MiyuYamasaki-Davis/EE-Emerge-2023-DancePad/pictures/Encasement/IMG_6620 2.JPG

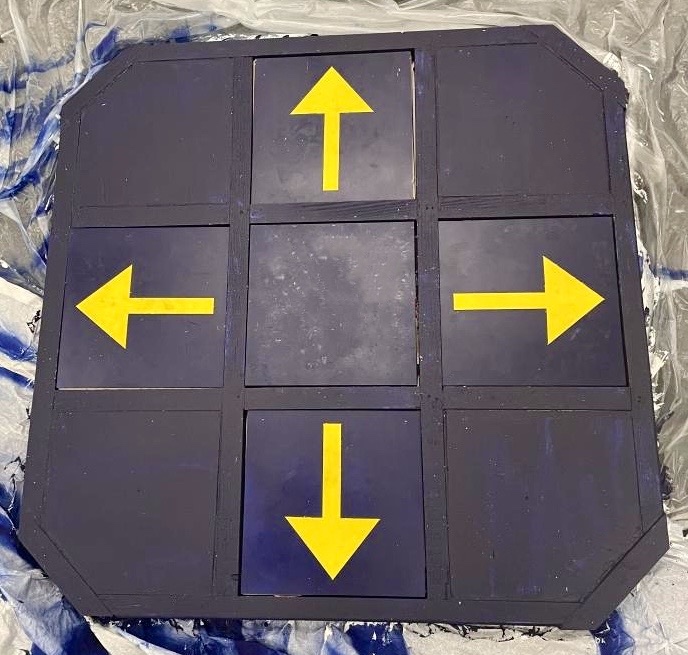
pictures/Encasement/IMG_6620 2.JPG
