MiyuYamasaki-Davis/EE-Emerge-2023-DancePad/pictures/Encasement/paintedBoard.JPG

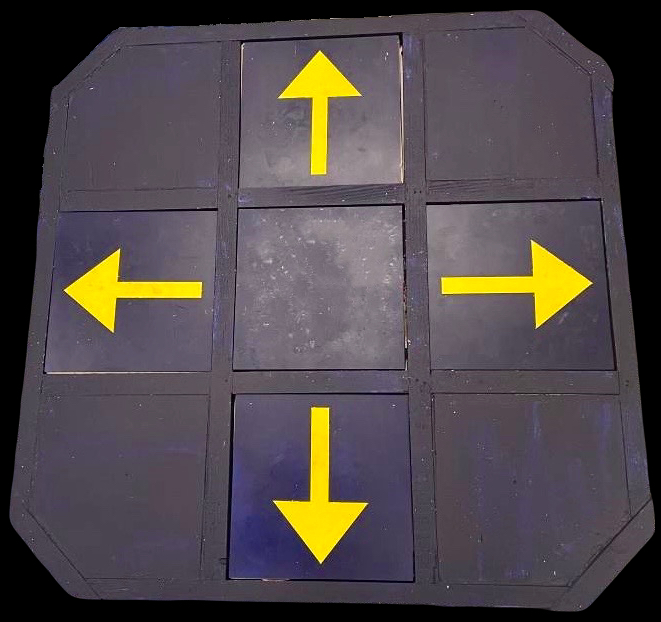
pictures/Encasement/paintedBoard.JPG
