MiyuYamasaki-Davis/EE-Emerge-2023-DancePad/pictures/Encasement/v1 plate sample.jpg

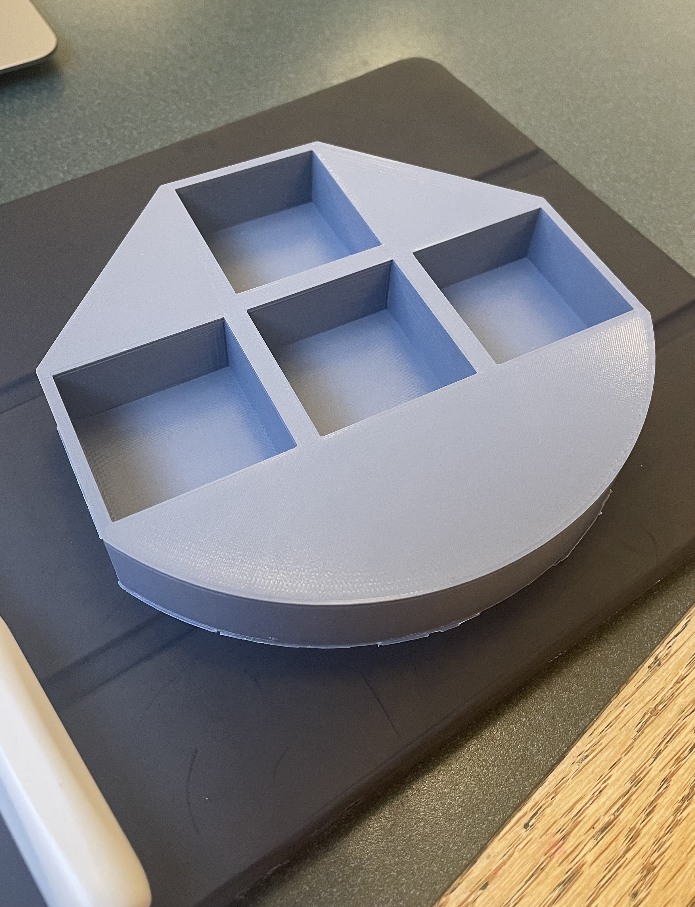
pictures/Encasement/v1 plate sample.jpg
