MiyuYamasaki-Davis/EE-Emerge-2023-DancePad/pictures/Encasement/v2 plate model.png

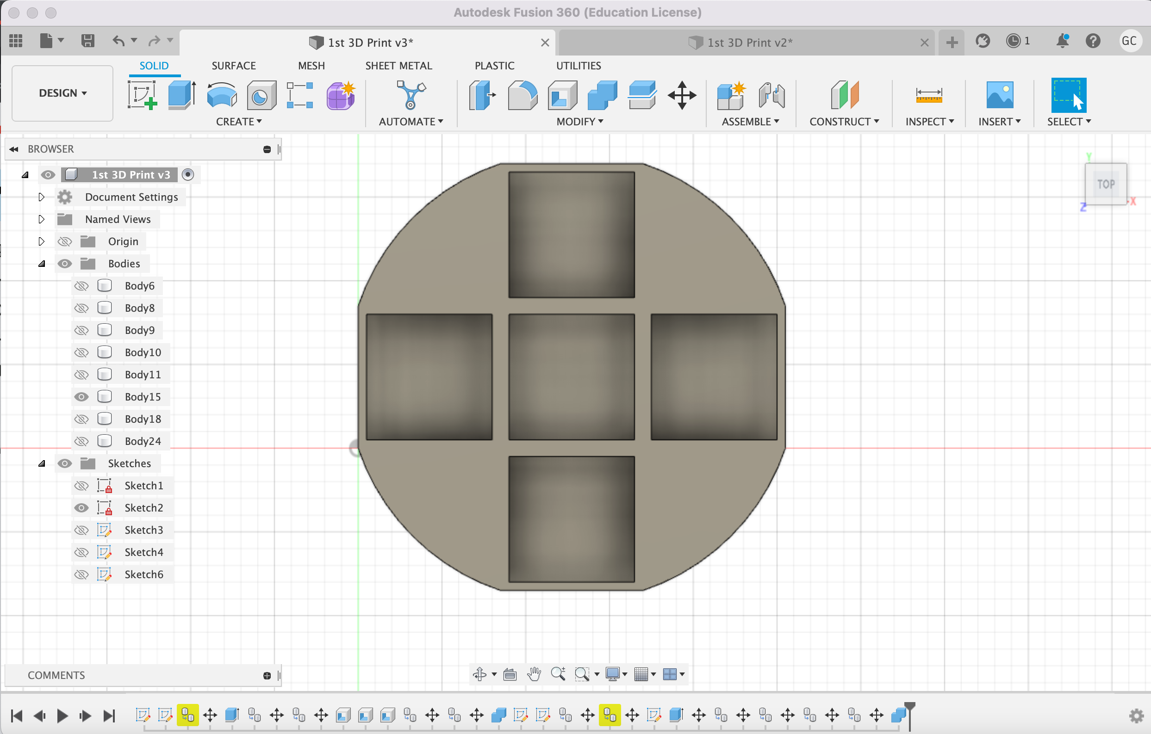
pictures/Encasement/v2 plate model.png
