MiyuYamasaki-Davis/EE-Emerge-2023-DancePad/pictures/Encasement/v3 platform design finished.jpg

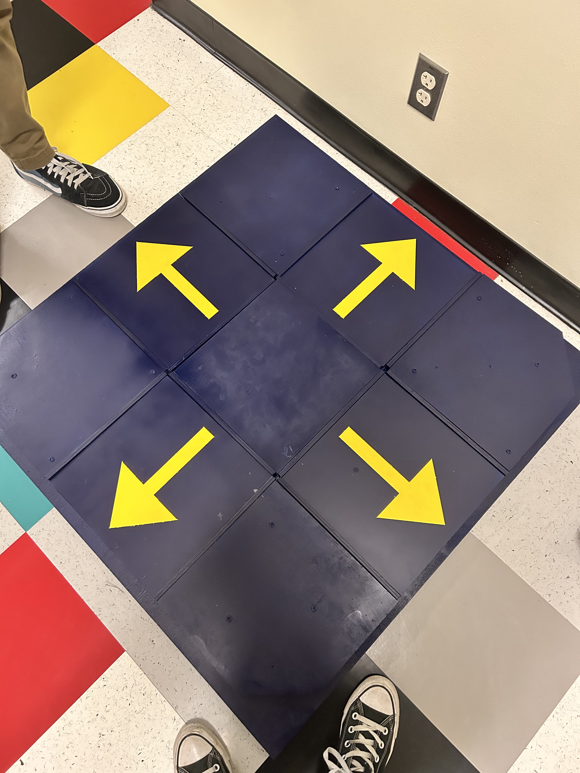
pictures/Encasement/v3 platform design finished.jpg
