MiyuYamasaki-Davis/EE-Emerge-2023-DancePad/pictures/Hardware/PCB v3 layout.png

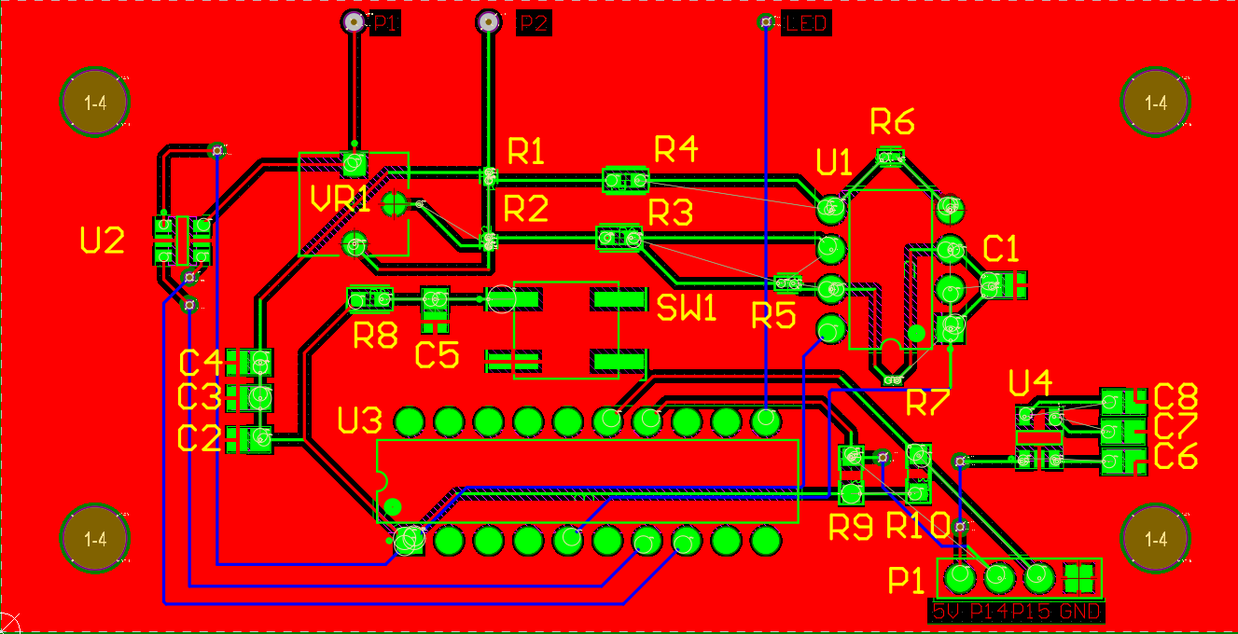
pictures/Hardware/PCB v3 layout.png
