MiyuYamasaki-Davis/EE-Emerge-2023-DancePad/pictures/Hardware/PCB v3 page 1.png

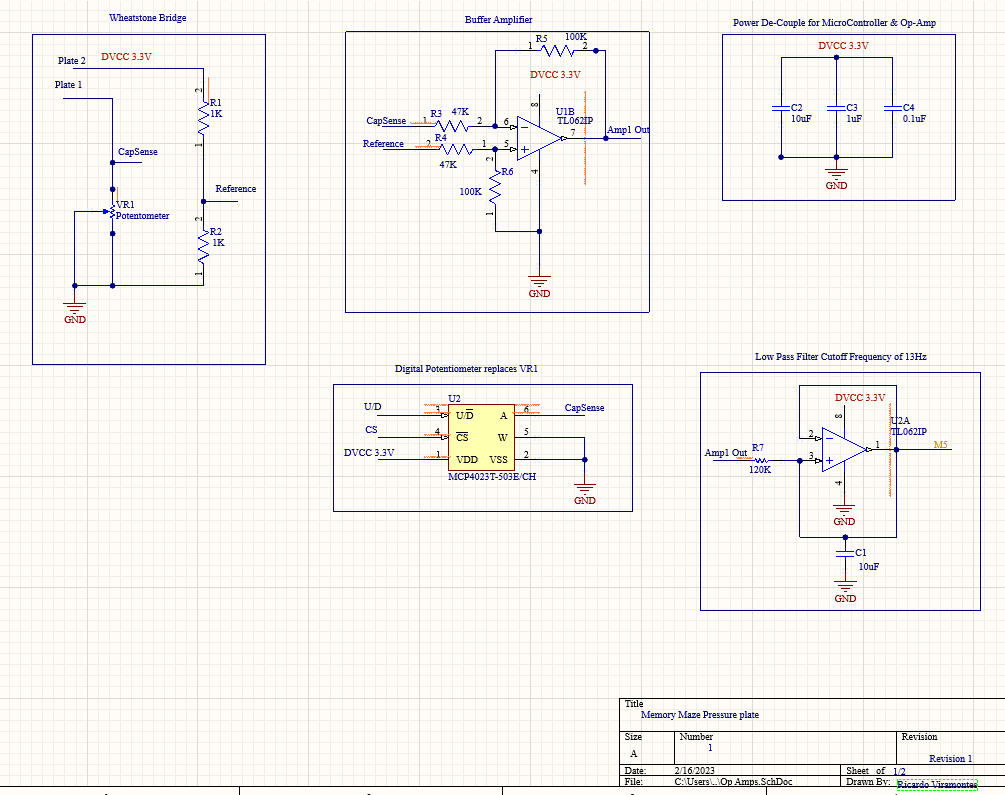
pictures/Hardware/PCB v3 page 1.png
