MiyuYamasaki-Davis/EE-Emerge-2023-DancePad/pictures/Hardware/PCB v4.jpg

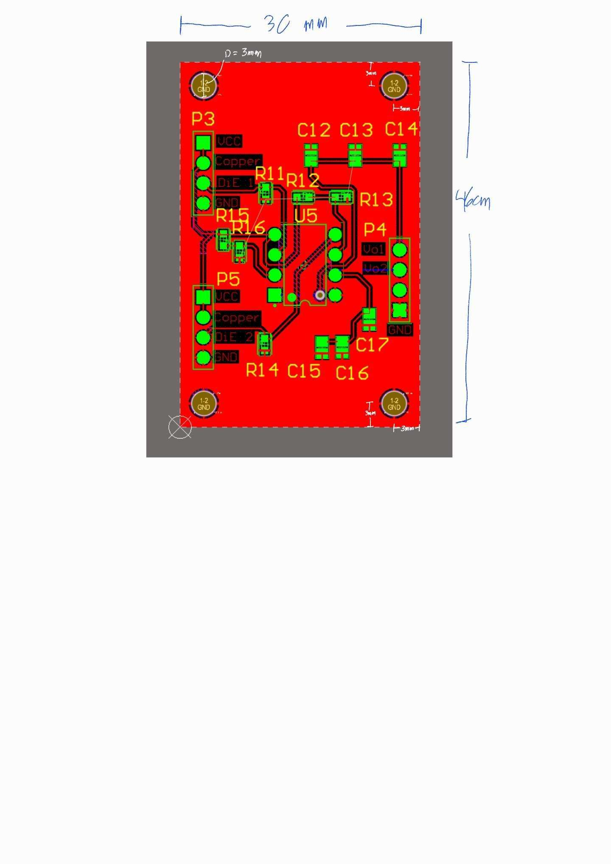
pictures/Hardware/PCB v4.jpg
