MiyuYamasaki-Davis/EE-Emerge-2023-DancePad/pictures/Hardware/Socket board backup of PCB v4.jpg

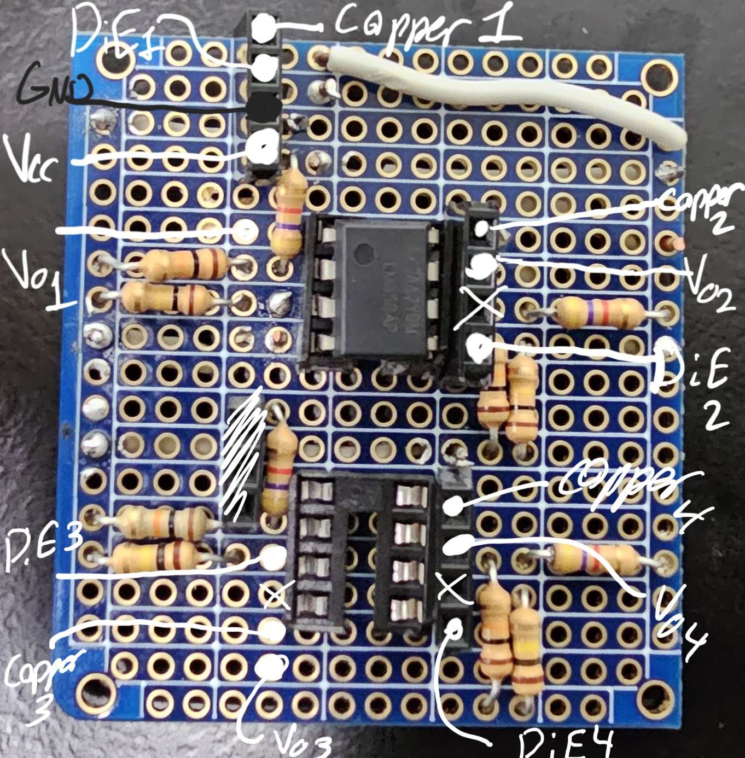
pictures/Hardware/Socket board backup of PCB v4.jpg
