MiyuYamasaki-Davis/EE-Emerge-2023-DancePad/pictures/Hardware/v1 PCB.png

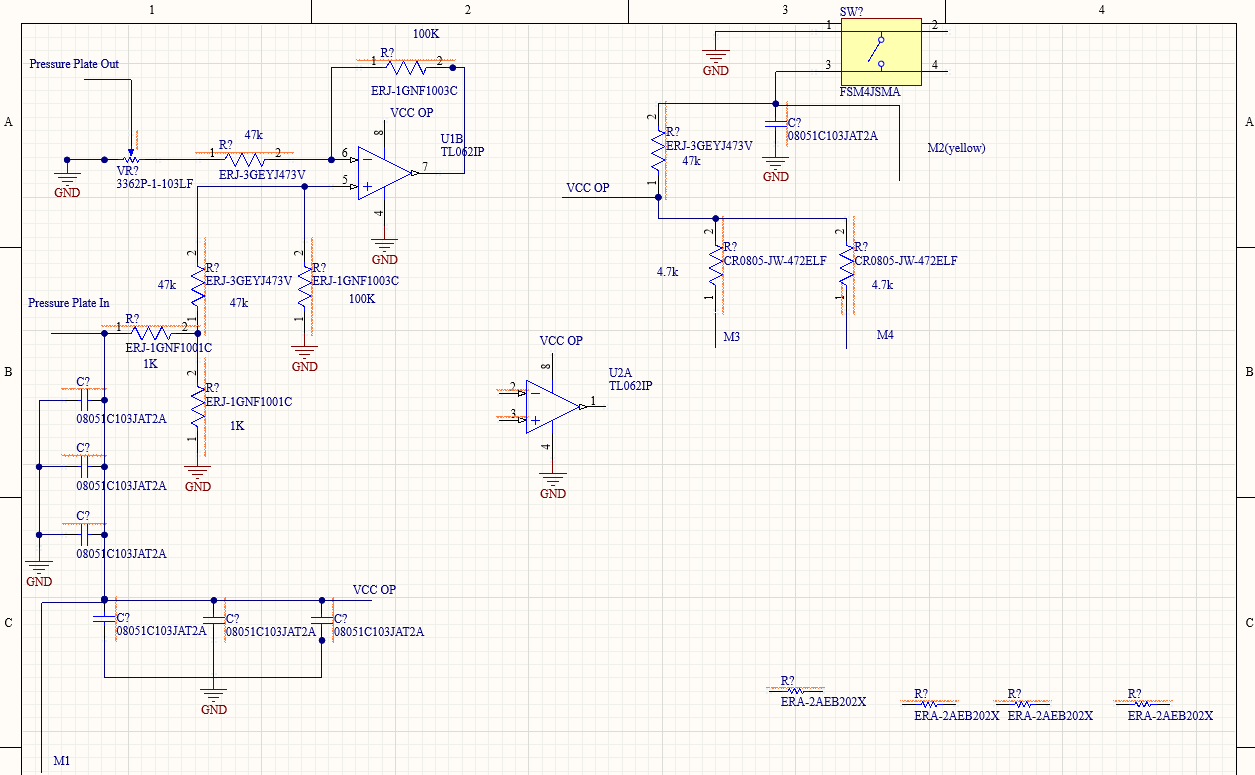
pictures/Hardware/v1 PCB.png
