MiyuYamasaki-Davis/EE-Emerge-2023-DancePad/pictures/Encasement/v3 plate design assembled.jpg

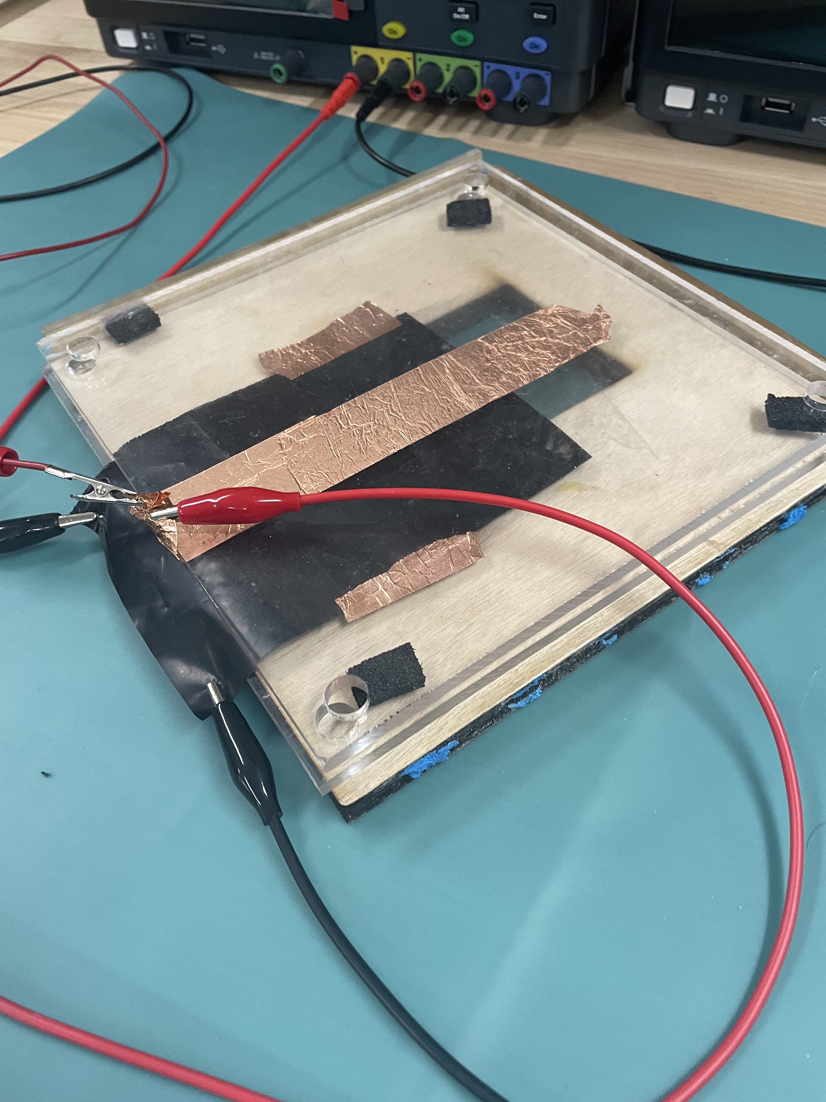
pictures/Encasement/v3 plate design assembled.jpg
