MiyuYamasaki-Davis/EE-Emerge-2023-DancePad/pictures/Software/v1 test with no logic.png

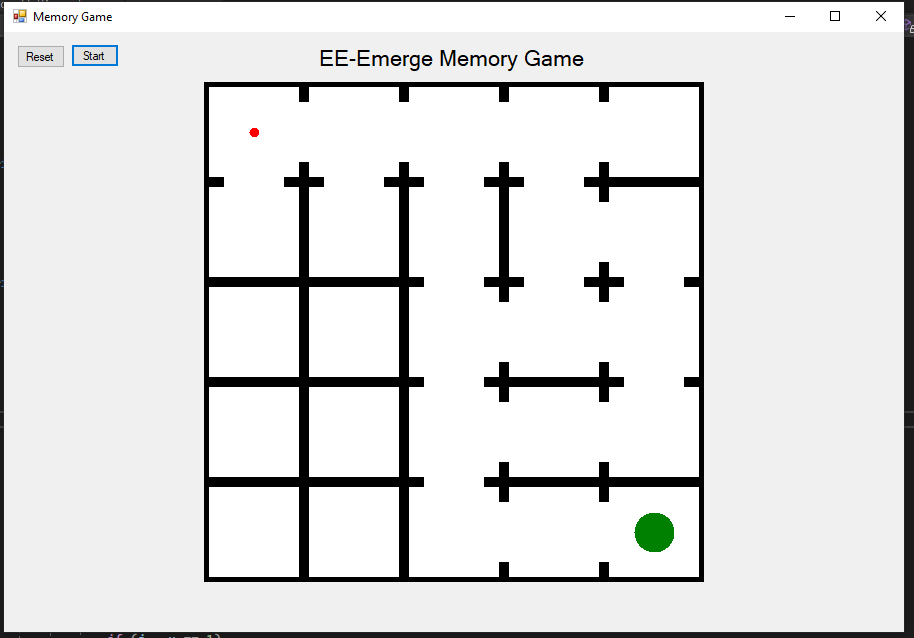
pictures/Software/v1 test with no logic.png
