MiyuYamasaki-Davis/EE-Emerge-2023-DancePad/pictures/Software/v2 test with logic.png

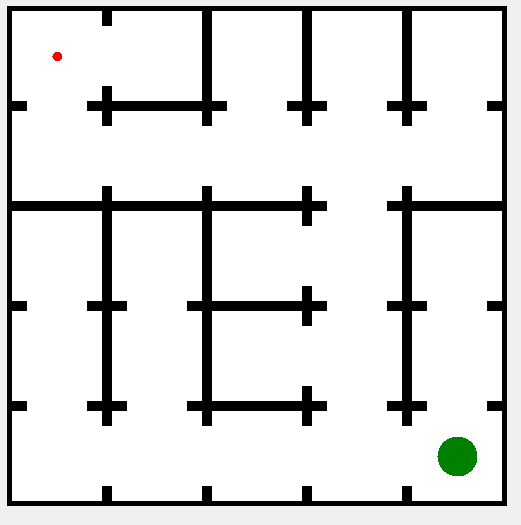
pictures/Software/v2 test with logic.png
