MiyuYamasaki-Davis/EE-Emerge-2023-DancePad/pictures/Software/v4 test.jpg

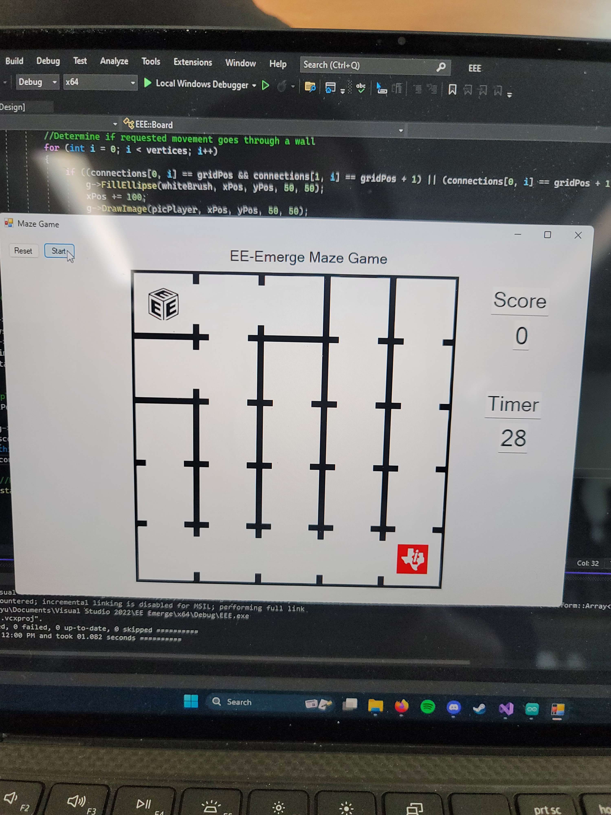
pictures/Software/v4 test.jpg
